PJTodd72/Plasma-Toroid-Driver/Toroid Generator.asc

C1: cap; 100p
C2: cap; 4.7n
C3: cap; {Coss}
C4: Cap; 10µ
D1: zener; MMBZ12VALY
L1: ind; 10µ
L2: ind; 2.6µ
R1: Res; 1000
R2: Res; 1000
R4: Res; 7500
R5: Res; {r}
U1: irfp260n
U2: SMBJ15CA
V1: voltage; 20
Named nets: 0
.tran 0 500u .1u uic
.params r =  4700
.params Coss = 603p
Changing Coss will change the output voltage 
of the ocsillating circuit, 603pF will result in a coltage of around 
1.2kV, 1.8nF will give 2kV
The plasma will no doubt effect this but I don't know how to
simulate that.
You can easily change the resonating frequency by simply
changing the capacitane of the caps on the right while ensuring
they keep the same ratio to each other as f = 1/sqrt(LC) doubling 
frequency will require 1/4 capacitance
